nekocharm/HoloCubic/3.Software/HoloCubic/holocubic.png

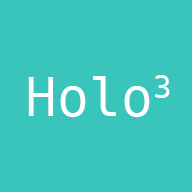
3.Software/HoloCubic/holocubic.png
