nekocharm/HoloCubic/3.Software/LvglSimulator/vs2019_proj/lv_examples/src/lv_ex_widgets/lv_ex_gauge/lv_ex_gauge_2.png

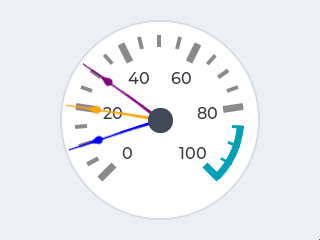
3.Software/LvglSimulator/vs2019_proj/lv_examples/src/lv_ex_widgets/lv_ex_gauge/lv_ex_gauge_2.png
