nekocharm/HoloCubic/3.Software/LvglSimulator/vs2019_proj/lv_examples/src/lv_ex_widgets/lv_ex_spinner/lv_ex_spinner_1.png

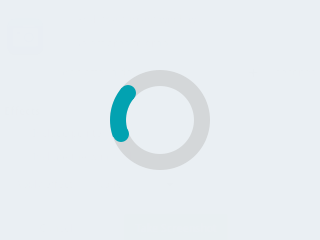
3.Software/LvglSimulator/vs2019_proj/lv_examples/src/lv_ex_widgets/lv_ex_spinner/lv_ex_spinner_1.png
