nekocharm/HoloCubic/3.Software/LvglSimulator/vs2019_proj/lv_examples/src/lv_ex_widgets/lv_ex_textarea/lv_ex_textarea_3.png

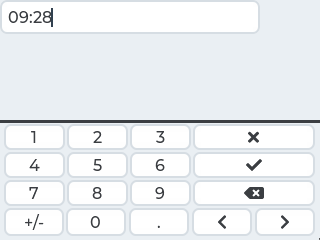
3.Software/LvglSimulator/vs2019_proj/lv_examples/src/lv_ex_widgets/lv_ex_textarea/lv_ex_textarea_3.png
