nekocharm/HoloCubic/4.3D Model/holocubic2.jpg

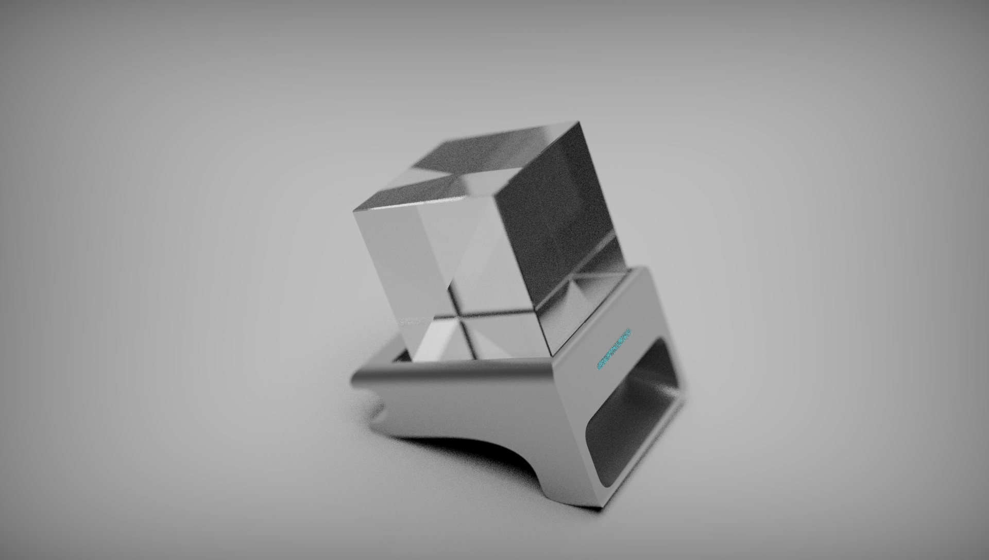
4.3D Model/holocubic2.jpg
