nekocharm/HoloCubic/4.3D Model/holocubic3.jpg

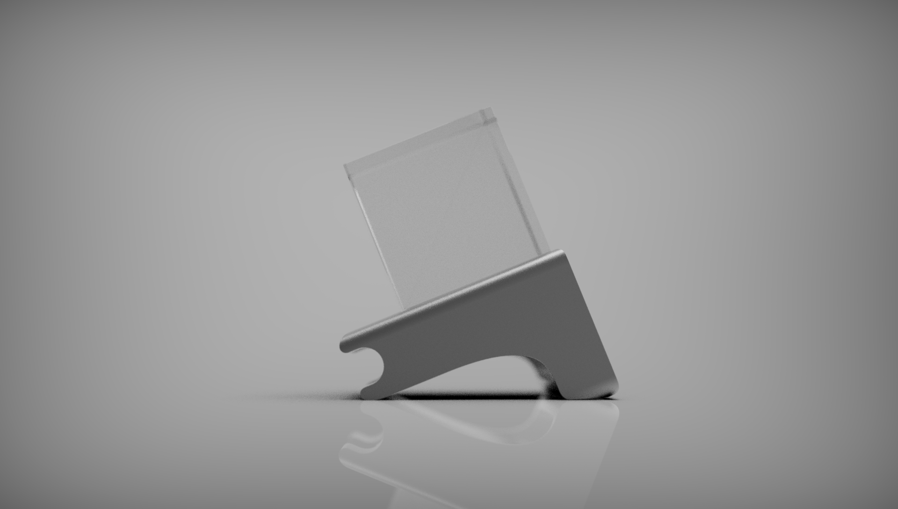
4.3D Model/holocubic3.jpg
