nekocharm/HoloCubic/2.Firmware/HoloCubic/src/lv_font_digital_72.c

/*
*---------------------------------------------------------------
*                        Lvgl Font Tool                         
*                                                               
* 注:使用unicode编码                                              
* 注:本字体文件由Lvgl Font Tool V0.4 生成                          
* 作者:阿里(qq:617622104)                                         
*---------------------------------------------------------------
*/


#include "lvgl.h"


static const uint8_t glyph_bitmap[] = {
/* 0 */
0x00,0x00,0x1c,0xff,0xff,0xff,0xff,0xff,0xff,0xff,0xfc,0x10,0x00,0x00,  //....+@@@@@@@@@@@@@@@@@+....
0x00,0x01,0xcf,0xff,0xff,0xff,0xff,0xff,0xff,0xff,0xff,0xc1,0x00,0x00,  //...+@@@@@@@@@@@@@@@@@@@+...
0x00,0x04,0xef,0xff,0xff,0xff,0xff,0xff,0xff,0xff,0xff,0xe4,0x00,0x00,  //...*@@@@@@@@@@@@@@@@@@@*...
0x01,0x50,0x5e,0xff,0xff,0xff,0xff,0xff,0xff,0xff,0xfe,0x50,0x51,0x00,  //.+*.*@@@@@@@@@@@@@@@@@*.*+.
0x1c,0xe5,0x05,0xef,0xff,0xff,0xff,0xff,0xff,0xff,0xe5,0x06,0xec,0x10,  //+@@*.*@@@@@@@@@@@@@@@*.*@@+
0xcf,0xfe,0x60,0x5e,0xff,0xff,0xff,0xff,0xff,0xfe,0x50,0x6e,0xff,0xc0,  //@@@@*.*@@@@@@@@@@@@@*.*@@@@
0xff,0xff,0xe6,0x05,0xaa,0xaa,0xaa,0xaa,0xaa,0xa5,0x06,0xef,0xff,0xf0,  //@@@@@*.*%%%%%%%%%%%*.*@@@@@
0xff,0xff,0xfe,0x50,0x00,0x00,0x00,0x00,0x00,0x00,0x6e,0xff,0xff,0xf0,  //@@@@@@*.............*@@@@@@
0xff,0xff,0xff,0xb0,0x00,0x00,0x00,0x00,0x00,0x00,0xbf,0xff,0xff,0xf0,  //@@@@@@@.............@@@@@@@
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
0x00,0x00,0x00,0x00,0x00,0x00,0x00,0x00,0x00,0x00,0xbf,0xff,0xff,0xf0,  //....................@@@@@@@
0x00,0x00,0x00,0x00,0x00,0x00,0x00,0x00,0x00,0x00,0xbf,0xff,0xff,0xf0,  //....................@@@@@@@
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


/* : */
0x00,0x09,0xa9,0x00,0x00,  //..+%%%+..
0x00,0xbf,0xff,0xb0,0x00,  //.+@@@@@+.
0x0b,0xff,0xff,0xfb,0x00,  //+@@@@@@@+
0xaf,0xff,0xff,0xff,0xa0,  //%@@@@@@@%
0x3e,0xff,0xff,0xfe,0x30,  //+@@@@@@@+
0x03,0xef,0xff,0xe3,0x00,  //.+@@@@@+.
0x00,0x2e,0xfe,0x20,0x00,  //..+@@@+..
0x00,0x00,0x00,0x00,0x00,  //.........
0x00,0x00,0x00,0x00,0x00,  //.........
0x00,0x00,0x00,0x00,0x00,  //.........
0x00,0x00,0x00,0x00,0x00,  //.........
0x00,0x00,0x00,0x00,0x00,  //.........
0x00,0x00,0x00,0x00,0x00,  //.........
0x00,0x00,0x00,0x00,0x00,  //.........
0x00,0x00,0x00,0x00,0x00,  //.........
0x00,0x00,0x00,0x00,0x00,  //.........
0x00,0x00,0x00,0x00,0x00,  //.........
0x00,0x00,0x00,0x00,0x00,  //.........
0x00,0x00,0x00,0x00,0x00,  //.........
0x00,0x00,0x00,0x00,0x00,  //.........
0x00,0x09,0xa9,0x00,0x00,  //..+%%%+..
0x00,0xbf,0xff,0xb0,0x00,  //.+@@@@@+.
0x0b,0xff,0xff,0xfb,0x00,  //+@@@@@@@+
0xaf,0xff,0xff,0xff,0xa0,  //%@@@@@@@%
0x3e,0xff,0xff,0xfe,0x30,  //+@@@@@@@+
0x03,0xef,0xff,0xe3,0x00,  //.+@@@@@+.
0x00,0x2e,0xfe,0x20,0x00,  //..+@@@+..


};


static const lv_font_fmt_txt_glyph_dsc_t glyph_dsc[] = {
    {.bitmap_index = 0,	.adv_w = 27, .box_h = 47, .box_w = 28, .ofs_x = 0, .ofs_y = 0},/*(0)*/
    {.bitmap_index = 658,	.adv_w = 27, .box_h = 41, .box_w = 8, .ofs_x = 20, .ofs_y = 3},/*(1)*/
    {.bitmap_index = 822,	.adv_w = 27, .box_h = 47, .box_w = 28, .ofs_x = 0, .ofs_y = 0},/*(2)*/
    {.bitmap_index = 1480,	.adv_w = 27, .box_h = 47, .box_w = 24, .ofs_x = 3, .ofs_y = 0},/*(3)*/
    {.bitmap_index = 2044,	.adv_w = 27, .box_h = 41, .box_w = 28, .ofs_x = 0, .ofs_y = 3},/*(4)*/
    {.bitmap_index = 2618,	.adv_w = 27, .box_h = 47, .box_w = 28, .ofs_x = 0, .ofs_y = 0},/*(5)*/
    {.bitmap_index = 3276,	.adv_w = 27, .box_h = 47, .box_w = 28, .ofs_x = 0, .ofs_y = 0},/*(6)*/
    {.bitmap_index = 3934,	.adv_w = 27, .box_h = 44, .box_w = 28, .ofs_x = 0, .ofs_y = 3},/*(7)*/
    {.bitmap_index = 4550,	.adv_w = 27, .box_h = 47, .box_w = 28, .ofs_x = 0, .ofs_y = 0},/*(8)*/
    {.bitmap_index = 5208,	.adv_w = 27, .box_h = 47, .box_w = 28, .ofs_x = 0, .ofs_y = 0},/*(9)*/
    {.bitmap_index = 5866,	.adv_w = 18, .box_h = 27, .box_w = 10, .ofs_x = 9, .ofs_y = 10},/*(:)*/
};


static const uint16_t unicode_list_1[] = {
    0x0030,	/*(0)*/
    0x0031,	/*(1)*/
    0x0032,	/*(2)*/
    0x0033,	/*(3)*/
    0x0034,	/*(4)*/
    0x0035,	/*(5)*/
    0x0036,	/*(6)*/
    0x0037,	/*(7)*/
    0x0038,	/*(8)*/
    0x0039,	/*(9)*/
    0x003a,	/*(:)*/
    0x0000,    /*End indicator*/
};


static const lv_font_fmt_txt_cmap_t cmaps[] = {
    {
        .range_start = 0x0030,
        .range_length = 0x003a,
        .type = LV_FONT_FMT_TXT_CMAP_SPARSE_TINY,
        .glyph_id_start = 0,
        .unicode_list = unicode_list_1,
        .glyph_id_ofs_list = NULL,
        .list_length = 11,
    }
};


static lv_font_fmt_txt_dsc_t font_dsc = {
    .glyph_bitmap = glyph_bitmap,
    .glyph_dsc = glyph_dsc,
    .cmaps = cmaps,
    .cmap_num = 1,
    .bpp = 4,

    .kern_scale = 0,
    .kern_dsc = NULL,
    .kern_classes = 0,

    .last_letter = 0x003a,
    .last_glyph_id = 10,
};


static int binsearch(const uint16_t *sortedSeq, int seqLength, uint16_t keyData) {
    int low = 0, mid, high = seqLength - 1;
    while (low <= high) {
        mid = (low + high)>>1;//右移1位等于是/2，奇数，无论奇偶，有个值就行
        if (keyData < sortedSeq[mid]) {
            high = mid - 1;//是mid-1，因为mid已经比较过了
        }
        else if (keyData > sortedSeq[mid]) {
            low = mid + 1;
        }
        else {
            return mid;
        }
    }
    return -1;
}


static const uint8_t * __user_font_get_bitmap(const lv_font_t * font, uint32_t unicode_letter) {
    lv_font_fmt_txt_dsc_t * fdsc = (lv_font_fmt_txt_dsc_t *) font->dsc;

    if( unicode_letter<fdsc->cmaps[0].range_start || unicode_letter>fdsc->cmaps[0].range_length ) return false;

    int i;
    if( unicode_letter==fdsc->last_letter ){
        i = fdsc->last_glyph_id;
    }
    else{
        i = binsearch(fdsc->cmaps[0].unicode_list, fdsc->cmaps[0].list_length, unicode_letter);
    }
    if( i != -1 ) {
        const lv_font_fmt_txt_glyph_dsc_t * gdsc = &fdsc->glyph_dsc[i];
        fdsc->last_glyph_id = i;
        fdsc->last_letter = unicode_letter;
        return &fdsc->glyph_bitmap[gdsc->bitmap_index];
    }
    return NULL;
}


static bool __user_font_get_glyph_dsc(const lv_font_t * font, lv_font_glyph_dsc_t * dsc_out, uint32_t unicode_letter, uint32_t unicode_letter_next) {
    lv_font_fmt_txt_dsc_t * fdsc = (lv_font_fmt_txt_dsc_t *) font->dsc;

    if( unicode_letter<fdsc->cmaps[0].range_start || unicode_letter>fdsc->cmaps[0].range_length ) return false;

    int i;
    if( unicode_letter==fdsc->last_letter ){
        i = fdsc->last_glyph_id;
    }
    else{
        i = binsearch(fdsc->cmaps[0].unicode_list, fdsc->cmaps[0].list_length, unicode_letter);
    }
    if( i != -1 ) {
        const lv_font_fmt_txt_glyph_dsc_t * gdsc = &fdsc->glyph_dsc[i];
        fdsc->last_glyph_id = i;
        fdsc->last_letter = unicode_letter;
        dsc_out->adv_w = gdsc->adv_w;
        dsc_out->box_h = gdsc->box_h;
        dsc_out->box_w = gdsc->box_w;
        dsc_out->ofs_x = gdsc->ofs_x;
        dsc_out->ofs_y = gdsc->ofs_y;
        dsc_out->bpp   = fdsc->bpp;
        return true;
    }
    return false;
}


//Digital Display,,-1
//字模高度：47
//内部字体
//使用排序和二分查表
lv_font_t lv_font_digital_72 = {
    .dsc = &font_dsc,
    .get_glyph_bitmap = __user_font_get_bitmap,
    .get_glyph_dsc = __user_font_get_glyph_dsc,
    .line_height = 72,
    .base_line = 0,
};
