nekocharm/HoloCubic/2.Firmware/HoloCubic/include/guider_fonts.h

#ifndef GUIDER_FONTS_H
#define GUIDER_FONTS_H
#ifdef __cplusplus
extern "C" {
#endif
    
#include "lv_font/lv_font.h"
    
LV_FONT_DECLARE(lv_font_simsun_12)
LV_FONT_DECLARE(lv_font_maiyuan_24)
LV_FONT_DECLARE(lv_font_maiyuan_32)
LV_FONT_DECLARE(lv_font_digital_48)
LV_FONT_DECLARE(lv_font_digital_72)

    
#ifdef __cplusplus
}
#endif
#endif
    
