nekocharm/HoloCubic/3.Software/LvglSimulator/vs2019_proj/lv_font_digital_48.c

/*
*---------------------------------------------------------------
*                        Lvgl Font Tool                         
*                                                               
* 注:使用unicode编码                                              
* 注:本字体文件由Lvgl Font Tool V0.4 生成                          
* 作者:阿里(qq:617622104)                                         
*---------------------------------------------------------------
*/


#include "lvgl/lvgl.h"


typedef struct{
    uint16_t min;
    uint16_t max;
    uint8_t  bpp;
    uint8_t  reserved[3];
}x_header_t;
typedef struct{
    uint32_t pos;
}x_table_t;
typedef struct{
    uint8_t adv_w;
    uint8_t box_w;
    uint8_t box_h;
    int8_t  ofs_x;
    int8_t  ofs_y;
    uint8_t r;
}glyph_dsc_t;


static const uint8_t glyph_dsc_xbf[] = {

0x31,0x00,0x3a,0x00,0x04,0x00,0x00,0x00,//xbf header

0x30,0x00,0x00,0x00,//0x0031
0xb2,0x00,0x00,0x00,//0x0032
0x18,0x02,0x00,0x00,//0x0033
0x89,0x03,0x00,0x00,//0x0034
0xc5,0x04,0x00,0x00,//0x0035
0x36,0x06,0x00,0x00,//0x0036
0xa7,0x07,0x00,0x00,//0x0037
0xed,0x08,0x00,0x00,//0x0038
0x5e,0x0a,0x00,0x00,//0x0039
0xcf,0x0b,0x00,0x00,//0x003a

/* 1 */
8,8,31,0,0,0,  //dsc : unicode = 0x0031
0x00,0x00,0x2c,0x20,  //....+@+.
0x00,0x00,0x9f,0xc0,  //....%@@.
0x00,0x02,0xef,0xe0,  //...+@@@+
0x00,0x08,0xff,0xd0,  //...%@@@.
0x00,0x0a,0xff,0xc0,  //...%@@@.
0x00,0x0c,0xff,0xa0,  //...@@@%.
0x00,0x0d,0xff,0x80,  //...@@@%.
0x00,0x0e,0xff,0x70,  //..+@@@*.
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
0x0e,0xff,0xff,0xff,0xff,0xff,0xff,0xf6,0xbf,0xe1,0x00,  //+@@@@@@@@@@@@@@*@@@+..
0x05,0xdf,0xff,0xff,0xff,0xff,0xff,0xfa,0x7e,0x60,0x00,  //.*@@@@@@@@@@@@@%%@*...
0x00,0x00,0x00,0x00,0x00,0x00,0x00,0x00,0x22,0x00,0x00,  //................++....


/* : */
7,6,17,1,0,0,  //dsc : unicode = 0x003a
0x00,0xef,0xf7,  //.+@@@*
0x01,0xff,0xf5,  //.+@@@*
0x03,0xff,0xf3,  //.+@@@*
0x00,0x00,0x00,  //......
0x00,0x00,0x00,  //......
0x00,0x00,0x00,  //......
0x00,0x00,0x00,  //......
0x00,0x00,0x00,  //......
0x00,0x00,0x00,  //......
0x00,0x00,0x00,  //......
0x00,0x00,0x00,  //......
0x00,0x00,0x00,  //......
0x00,0x00,0x00,  //......
0x00,0x00,0x00,  //......
0x6f,0xff,0x00,  //*@@@+.
0x8f,0xfd,0x00,  //%@@@..
0xaf,0xfc,0x00,  //%@@@..


};


static const uint8_t * __user_font_get_bitmap(const lv_font_t * font, uint32_t unicode_letter) {
    x_header_t *p_hd = (x_header_t*)&glyph_dsc_xbf[0];
    if( unicode_letter>p_hd->max || unicode_letter<p_hd->min ) {
        return NULL;
    }
    uint32_t unicode_offset = unicode_letter-p_hd->min;
    uint32_t *p_pos = (uint32_t *)&glyph_dsc_xbf[ sizeof(x_header_t) ];
    if( p_pos[unicode_offset] != 0 ) {
        return &glyph_dsc_xbf[ p_pos[unicode_offset]+sizeof(glyph_dsc_t) ];
    }
    return NULL;
}


static bool __user_font_get_glyph_dsc(const lv_font_t * font, lv_font_glyph_dsc_t * dsc_out, uint32_t unicode_letter, uint32_t unicode_letter_next) {
    x_header_t *p_hd = (x_header_t*)&glyph_dsc_xbf[0];
    if( unicode_letter>p_hd->max || unicode_letter<p_hd->min ) {
        return false;
    }
    uint32_t unicode_offset = unicode_letter-p_hd->min;
    uint32_t *p_pos = (uint32_t *)&glyph_dsc_xbf[ sizeof(x_header_t) ];
    if( p_pos[unicode_offset] != 0 ) {
        glyph_dsc_t * gdsc = (glyph_dsc_t*)&glyph_dsc_xbf[ p_pos[unicode_offset] ];
        dsc_out->adv_w = gdsc->adv_w;
        dsc_out->box_h = gdsc->box_h;
        dsc_out->box_w = gdsc->box_w;
        dsc_out->ofs_x = gdsc->ofs_x;
        dsc_out->ofs_y = gdsc->ofs_y;
        dsc_out->bpp   = p_hd->bpp;
        return true;
    }
    return false;
}


//Digital-7 Italic,,-1
//字模高度：26
//XBF字体,内部大数组
lv_font_t lv_font_digital_48 = {
    .get_glyph_bitmap = __user_font_get_bitmap,
    .get_glyph_dsc = __user_font_get_glyph_dsc,
    .line_height = 26,
    .base_line = 0,
};
