nekocharm/HoloCubic/3.Software/LvglSimulator/vs2019_proj/gui_guider.c

#include "lvgl/lvgl.h"
#include <stdio.h>
#include "gui_guider.h"


void setup_ui(lv_ui* ui)
{
	setup_scr();

	setup_scr_spaceman(ui);
	//setup_scr_home(ui);
	//lv_scr_load(ui->home);

	//setup_scr_scenes(ui);
	//lv_scr_load(ui->scenes);
}
